art-mon/orrery/firmware/main/als.c

#include "als.h"
#include "pins.h"
#include "panel.h"

#include <math.h>
#include <stdbool.h>
#include <stdint.h>

// Cached values exposed via als_get_lux / als_get_factor. Written only by
// the ALS task, read by scenes on the render task. A torn read is fine —
// worst case a display shows a stale-by-one-sample number for one frame.
static float s_last_lux    = NAN;
static float s_last_factor = 0.0f;

float als_get_lux(void)    { return s_last_lux; }
float als_get_factor(void) { return s_last_factor; }

#include <driver/i2c_master.h>
#include <esp_log.h>
#include <freertos/FreeRTOS.h>
#include <freertos/task.h>

static const char *TAG = "als";

// BH1750 command bytes and timing (see Rohm datasheet, rev.D).
#define BH1750_ADDR              0x23
#define BH1750_POWER_ON          0x01
#define BH1750_ONE_SHOT_HIRES    0x20   // 1 lux resolution, ~180 ms max
#define BH1750_MEAS_WAIT_MS      180

// Cadence. The BH1750 needs ~180 ms per one-shot high-res read, but the
// filter and brightness write tick faster so the eye sees a smooth ramp
// instead of 200 ms staircase steps.
#define SAMPLE_PERIOD_MS         200
#define TICK_MS                  20
#define SAMPLE_TICKS             (SAMPLE_PERIOD_MS / TICK_MS)     // 10
#define MEAS_READ_TICK           (BH1750_MEAS_WAIT_MS / TICK_MS)  // 9
#define TAU_S                    3.0f   // 1-pole LPF time constant
// α = dt / (τ + dt) — computed from TICK_MS so τ is invariant to cadence.

// Log-linear lux → factor map.
// Below LUX_LO the brightness sits at the floor; above LUX_HI it's full max.
// Anchored so a normal-lit room (≥ LUX_HI) sits at the ceiling and mild
// shading (≤ LUX_LO) hits the floor — otherwise the interior of the curve
// eats most of the dynamic range.
#define LUX_LO                   15.0f
#define LUX_HI                   80.0f
#define FACTOR_FLOOR             0.025f  // ≈ 1/40 — never fully off
#define FACTOR_CEIL              1.0f

static i2c_master_bus_handle_t s_bus  = NULL;
static i2c_master_dev_handle_t s_dev  = NULL;

static esp_err_t als_trigger_measurement(void) {
    const uint8_t cmd = BH1750_ONE_SHOT_HIRES;
    return i2c_master_transmit(s_dev, &cmd, 1, 100);
}

static esp_err_t als_read_lux(float *lux_out) {
    uint8_t buf[2] = {0};
    esp_err_t err = i2c_master_receive(s_dev, buf, sizeof(buf), 100);
    if (err != ESP_OK) return err;
    uint16_t raw = ((uint16_t)buf[0] << 8) | buf[1];
    *lux_out = (float)raw / 1.2f;
    return ESP_OK;
}

static float lux_to_factor(float lux) {
    if (lux <= LUX_LO) return FACTOR_FLOOR;
    if (lux >= LUX_HI) return FACTOR_CEIL;
    // Interpolate on log10 so the curve matches perceived brightness.
    float t = (log10f(lux) - log10f(LUX_LO)) / (log10f(LUX_HI) - log10f(LUX_LO));
    return FACTOR_FLOOR + (FACTOR_CEIL - FACTOR_FLOOR) * t;
}

static void als_task(void *arg) {
    const uint8_t max_brightness = (uint8_t)(uintptr_t)arg;

    // α at TICK_MS cadence (τ = 3 s, dt = 20 ms → α ≈ 0.0066). Small α + fast
    // ticks → sub-unit brightness updates → smooth visual ramp.
    const float alpha = (float)TICK_MS / 1000.0f
                     / (TAU_S + (float)TICK_MS / 1000.0f);

    // Filter state (< 0 means "not seeded yet"). Target updates every SAMPLE_TICKS.
    float filtered = -1.0f;
    float target   = FACTOR_CEIL;
    bool  trigger_ok = false;
    int   log_countdown = 0;
    int   sample_phase = 0;   // 0..SAMPLE_TICKS-1
    int   last_applied = -1;  // last brightness written to the panel

    TickType_t last_wake = xTaskGetTickCount();
    while (true) {
        // Kick off a new BH1750 measurement at the start of each sample window.
        if (sample_phase == 0) {
            esp_err_t err = als_trigger_measurement();
            trigger_ok = (err == ESP_OK);
            if (!trigger_ok) {
                ESP_LOGW(TAG, "BH1750 trigger err 0x%x — holding target", err);
            }
        }

        // Read the result ~180 ms later, once the sensor's integration is done.
        if (sample_phase == MEAS_READ_TICK && trigger_ok) {
            float lux = 0.0f;
            esp_err_t err = als_read_lux(&lux);
            if (err == ESP_OK) {
                target = lux_to_factor(lux);
                if (filtered < 0.0f) filtered = target;
                s_last_lux = lux;
                if (--log_countdown <= 0) {
                    int b_now = (int)lroundf((float)max_brightness * filtered);
                    ESP_LOGI(TAG, "lux=%.1f target=%.2f filt=%.2f b=%d/%u",
                             lux, target, filtered, b_now, max_brightness);
                    log_countdown = 5;  // ~1 log/sec at a 200 ms sample cadence
                }
            } else {
                ESP_LOGW(TAG, "BH1750 read err 0x%x — holding target", err);
            }
        }

        // Every tick: step the LPF; only write to the panel when the rounded
        // brightness actually changes. The driver's set_brightness rewrites the
        // OE bits across every DMA buffer, so calling it at 50 Hz thrashes the
        // panel and can block a full blank at b=0.
        if (filtered >= 0.0f) {
            filtered += alpha * (target - filtered);
            s_last_factor = filtered;
            int b = (int)lroundf((float)max_brightness * filtered);
            if (b < 1) b = 1;
            if (b > max_brightness) b = max_brightness;
            if (b != last_applied) {
                panel_set_brightness((uint8_t)b);
                last_applied = b;
            }
        }

        sample_phase = (sample_phase + 1) % SAMPLE_TICKS;
        vTaskDelayUntil(&last_wake, pdMS_TO_TICKS(TICK_MS));
    }
}

void als_start(uint8_t max_brightness) {
    i2c_master_bus_config_t bus_cfg = {
        .clk_source                   = I2C_CLK_SRC_DEFAULT,
        .i2c_port                     = I2C_NUM_0,
        .sda_io_num                   = PIN_I2C_SDA,
        .scl_io_num                   = PIN_I2C_SCL,
        .glitch_ignore_cnt            = 7,
        .flags.enable_internal_pullup = true,
    };
    ESP_ERROR_CHECK(i2c_new_master_bus(&bus_cfg, &s_bus));

    i2c_device_config_t dev_cfg = {
        .dev_addr_length = I2C_ADDR_BIT_LEN_7,
        .device_address  = BH1750_ADDR,
        .scl_speed_hz    = 100000,
    };
    ESP_ERROR_CHECK(i2c_master_bus_add_device(s_bus, &dev_cfg, &s_dev));

    // Power-on ping; harmless if the sensor is absent (task will log I/O errors).
    const uint8_t power_on = BH1750_POWER_ON;
    esp_err_t err = i2c_master_transmit(s_dev, &power_on, 1, 100);
    if (err != ESP_OK) {
        ESP_LOGW(TAG, "BH1750 power-on failed 0x%x — check wiring", err);
    } else {
        ESP_LOGI(TAG, "BH1750 online @ 0x%02x — max brightness cap = %u",
                 BH1750_ADDR, max_brightness);
    }

    xTaskCreate(als_task, "als", 3072, (void *)(uintptr_t)max_brightness, 3, NULL);
}
