art-mon/orrery/firmware/main/panel.cpp

#include "panel.h"
#include "pins.h"
#include "font.h"

#include "hub75.h"

static Hub75Driver *s_panel = nullptr;
static uint8_t s_last_brightness = 0;

void panel_init(void) {
    Hub75Config cfg{};
    cfg.panel_width  = PANEL_W;
    cfg.panel_height = PANEL_H;
    cfg.scan_wiring  = Hub75ScanWiring::STANDARD_TWO_SCAN;  // panel marked "16s" = 1:16 scan
    cfg.shift_driver = Hub75ShiftDriver::FM6126A;           // try FM6126A first; fall back to GENERIC
    cfg.double_buffer = true;                               // tear-free animation

    cfg.pins.r1  = PIN_R1;
    cfg.pins.g1  = PIN_G1;
    cfg.pins.b1  = PIN_B1;
    cfg.pins.r2  = PIN_R2;
    cfg.pins.g2  = PIN_G2;
    cfg.pins.b2  = PIN_B2;
    cfg.pins.a   = PIN_A;
    cfg.pins.b   = PIN_B;
    cfg.pins.c   = PIN_C;
    cfg.pins.d   = PIN_D;
    cfg.pins.e   = PIN_E;
    cfg.pins.lat = PIN_LAT;
    cfg.pins.oe  = PIN_OE;
    cfg.pins.clk = PIN_CLK;

    s_panel = new Hub75Driver(cfg);
    s_panel->begin();
    s_panel->clear();
}

void panel_clear(void) {
    if (s_panel) s_panel->clear();
}

void panel_flip(void) {
    if (s_panel) s_panel->flip_buffer();
}

void panel_set_brightness(uint8_t b) {
    if (s_panel) s_panel->set_brightness(b);
    s_last_brightness = b;
}

uint8_t panel_get_brightness(void) {
    return s_last_brightness;
}

void panel_draw_test_pattern(void) {
    if (!s_panel) return;
    s_panel->clear();

    // White border
    s_panel->fill(0, 0, PANEL_W, 1, 255, 255, 255);
    s_panel->fill(0, PANEL_H - 1, PANEL_W, 1, 255, 255, 255);
    s_panel->fill(0, 0, 1, PANEL_H, 255, 255, 255);
    s_panel->fill(PANEL_W - 1, 0, 1, PANEL_H, 255, 255, 255);

    // RGB bars — verify channel ordering
    s_panel->fill(2,  2, 20, 8, 255, 0,   0);
    s_panel->fill(22, 2, 20, 8, 0,   255, 0);
    s_panel->fill(42, 2, 20, 8, 0,   0,   255);

    // Diagonal across both halves — verifies row addressing
    for (int i = 0; i < PANEL_H; ++i) {
        s_panel->set_pixel(i * 2, i, 255, 200, 0);
    }
}

void panel_pixel(int x, int y, uint8_t r, uint8_t g, uint8_t b) {
    if (!s_panel) return;
    if (x < 0 || y < 0 || x >= PANEL_W || y >= PANEL_H) return;
    s_panel->set_pixel((uint16_t)x, (uint16_t)y, r, g, b);
}

int panel_draw_text(int x, int y, const char *s, uint8_t r, uint8_t g, uint8_t b) {
    if (!s_panel || !s) return x;
    for (const char *p = s; *p; ++p) {
        const uint8_t *g5 = font_glyph(*p);
        for (int col = 0; col < FONT_W; ++col) {
            uint8_t bits = g5[col];
            for (int row = 0; row < FONT_H; ++row) {
                if (bits & (1u << row)) panel_pixel(x + col, y + row, r, g, b);
            }
        }
        x += FONT_ADVANCE;
    }
    return x;
}
