art-mon/orrery/firmware/main/panel.h

#pragma once

#include <stdint.h>

#ifdef __cplusplus
extern "C" {
#endif

void panel_init(void);
void panel_clear(void);
void panel_set_brightness(uint8_t b);
uint8_t panel_get_brightness(void);
void panel_draw_test_pattern(void);

// Atomically swap the back buffer (what we've been drawing into) with the
// front buffer (what the DMA is scanning out). Call once per frame, after
// all drawing is done, to avoid tearing.
void panel_flip(void);

// Draw a single pixel (RGB888). Coordinates outside the panel are clipped.
void panel_pixel(int x, int y, uint8_t r, uint8_t g, uint8_t b);

// Draw an ASCII string in 5x7 font at (x, y) (top-left of the glyph cell).
// Returns the advance (final cursor x).
int  panel_draw_text(int x, int y, const char *s, uint8_t r, uint8_t g, uint8_t b);

#ifdef __cplusplus
}
#endif
