art-mon/orrery/firmware/main/wifi.c

#include "wifi.h"
#include "wifi_creds.h"

#include <string.h>
#include <esp_event.h>
#include <esp_log.h>
#include <esp_netif.h>
#include <esp_wifi.h>
#include <freertos/FreeRTOS.h>
#include <freertos/event_groups.h>
#include <nvs_flash.h>

static const char *TAG = "wifi";

static EventGroupHandle_t s_events;
#define BIT_CONNECTED  BIT0
#define BIT_FAILED     BIT1

static void event_handler(void *arg, esp_event_base_t base, int32_t id, void *data) {
    if (base == WIFI_EVENT && id == WIFI_EVENT_STA_START) {
        esp_wifi_connect();
    } else if (base == WIFI_EVENT && id == WIFI_EVENT_STA_DISCONNECTED) {
        ESP_LOGW(TAG, "disconnected, retrying");
        esp_wifi_connect();
    } else if (base == IP_EVENT && id == IP_EVENT_STA_GOT_IP) {
        ip_event_got_ip_t *ev = (ip_event_got_ip_t *)data;
        ESP_LOGI(TAG, "got IP " IPSTR, IP2STR(&ev->ip_info.ip));
        xEventGroupSetBits(s_events, BIT_CONNECTED);
    }
}

bool wifi_start_and_wait(uint32_t timeout_ms) {
    esp_err_t err = nvs_flash_init();
    if (err == ESP_ERR_NVS_NO_FREE_PAGES || err == ESP_ERR_NVS_NEW_VERSION_FOUND) {
        ESP_ERROR_CHECK(nvs_flash_erase());
        ESP_ERROR_CHECK(nvs_flash_init());
    }

    ESP_ERROR_CHECK(esp_netif_init());
    ESP_ERROR_CHECK(esp_event_loop_create_default());
    esp_netif_create_default_wifi_sta();

    wifi_init_config_t cfg = WIFI_INIT_CONFIG_DEFAULT();
    ESP_ERROR_CHECK(esp_wifi_init(&cfg));

    s_events = xEventGroupCreate();
    ESP_ERROR_CHECK(esp_event_handler_register(WIFI_EVENT, ESP_EVENT_ANY_ID, &event_handler, NULL));
    ESP_ERROR_CHECK(esp_event_handler_register(IP_EVENT,   IP_EVENT_STA_GOT_IP, &event_handler, NULL));

    wifi_config_t wc = {0};
    strlcpy((char *)wc.sta.ssid,     WIFI_SSID, sizeof(wc.sta.ssid));
    strlcpy((char *)wc.sta.password, WIFI_PASS, sizeof(wc.sta.password));
    wc.sta.threshold.authmode = WIFI_AUTH_WPA2_PSK;

    ESP_ERROR_CHECK(esp_wifi_set_mode(WIFI_MODE_STA));
    ESP_ERROR_CHECK(esp_wifi_set_config(WIFI_IF_STA, &wc));
    ESP_ERROR_CHECK(esp_wifi_start());

    ESP_LOGI(TAG, "connecting to \"%s\"", WIFI_SSID);
    EventBits_t bits = xEventGroupWaitBits(
        s_events, BIT_CONNECTED | BIT_FAILED,
        pdFALSE, pdFALSE, pdMS_TO_TICKS(timeout_ms));

    return (bits & BIT_CONNECTED) != 0;
}
